helixzz/rdimm-hdd-case/docs/v3.2-rc1.zh-CN.md

# v3.2-rc1：带明确支撑配置的打印可靠性修订

这是针对 v3.1 外壳按压锁扣粘连反馈的**实测中的候选版**。保留 8 条容量、2+3+3 三层一体托盘、147 × 101.6 × 26 mm 外形和按下后滑开的盖板；日常使用仍不需要内部螺丝或独立限位框。此版本没有做提速优化。检查件已打印并拆除全部支撑，但清理依赖工具和技巧；完整套件、锁扣功能、力度及寿命仍未验证。

## 改动

最新实测发现 A 小样缺少下承托，盖板会倾斜下落；弹臂回弹正常。单槽实际 DIMM 装卸无干涉但固定力偏弱。参见 [实物记录](validation-v3.2-rc1.md) 及 [仅修正 A 底座的 RC2](v3.2-rc2-latch-check.zh-CN.md)，不要将原 A 的切片通过等同于锁定功能通过。

1. **外壳锁扣：**移除与弹臂仅隔 0.2 mm 的平行护挡，将弹臂横向宽度从 0.8 增至 1.6 mm。保留根部、锁齿位置和按下释放方向。相邻护挡粘连的几何条件已消除，但弹臂仍需打印支撑；移除护挡也改变了承力方式，不能据此声称携带保持力或疲劳寿命已提高。
2. **托盘槽口：**PCB 支撑高度仍为 3.0 mm，挡齿下表面从 4.5 调整到 4.6 mm；名义槽高从 1.5 增至 1.6 mm。按参考最厚 PCB 1.37 mm，名义高度余量由 0.13 增至 0.23 mm。固定槽和活动齿入口增加约 0.4 mm 长、0.3 mm 高的导入斜面。斜面帮助对准，不表示可以用内存强压扣入。
3. **装配空间：**没有降低底托盘 PCB 支撑面，避免与外壳背板凹区的顶面冲突；没有填死底托盘的背板避让凹区。最不利参考颗粒包络下方仍留约 0.3 mm，向上顶到新止挡时与下一层底面约留 0.1 mm，须用实际内存核对。不得再自行放大槽高或整体缩放。
4. **打印支撑：**工程开启普通贴合支撑，允许支撑从模型表面开始，支撑顶/底 Z 间距 0.2 mm、XY 间距 0.35 mm、顶部接触层 3 层、接触层间距 0.25 mm，同材料打印。逐区检查了外壳弹臂、外壳接口凹区、底托盘约 40 mm 的悬空凹区，以及 8 个槽的固定槽/活动齿下方的支撑路径。

## 文件选择

带 `P2S-PLA-Basic` 后缀的 3MF 是**包含机器、材料、工艺设置的可编辑 Bambu Studio 工程**；需以“打开工程”方式打开，保留配置后切片。它不是已发送的打印任务，也不是 G-code。配套支持配置从本机安装的公开官方预设生成，不含用户打印机连接资料。

仓库 `models/v3.2-rc1/` 的普通 STL/3MF **只含几何**；`profiles/v3.2-rc1-supports.json` 是可复用工艺。不能只导入几何后继续使用关闭支撑的旧工艺。重建带设置工程的方法见下方命令。

| 盘名 | 内容 | P2S / PLA Basic 估算 | 选择方式 |
|---|---|---:|---|
| `plate-0-checks` | 单槽托盘、外壳锁扣底座和滑块、底托盘凹区局部，共 4 件 | 约 31 分钟 / 13.7 g | 可选验证盘，一次打印覆盖主要风险 |
| `plate-1-body-only` | 新外壳 | 约 90 分钟 / 62.7 g | 已有完好 v3.1 盖板时选它 |
| `plate-2-all-trays` | 底/中/顶三张新托盘 | 约 81 分钟 / 46.7 g | 完整托盘盘，只需一次打印 |
| `plate-1-pin-clearance` | 新外壳和盖板 | 约 117 分钟 / 87.0 g | 从零制作整套时选它，替代 body-only |

完整五件仍为 **两盘**；可选验证盘不算生产零件，也不能装入正式盒子。每盘 STL 和 3MF 二选一，不要导入两遍。打印方向已固定，100% 比例，按层打印。

已有 v3.1 盖板的几何不变，可保留并与新外壳试装；旧外壳的失效锁扣不会被新托盘修复。新托盘应使用整套。插入硬盘槽的孔位、接口避让和真实 DIMM 布局仍须实物确认。

上述时间来自 Bambu Studio 02.08.02.61 的切片估算，含估算准备时间，不含换盘、冷却、拆支撑；不是实测承诺。工艺保持 0.20 mm、2 道墙、15% Grid、45° 填充方向、5 层/1.0 mm 顶部、3 层底部与 Classic 墙生成器。PLA Pure 应选择对应的实际耗材预设后重新切片，保留支撑工艺；不能把 PLA Basic 的温度或时间直接当作 PLA Pure 的结果。

## 打印与清理

检查件已实际打印并成功拆除全部支撑；A 接触紧密，B/C 需镊子和技巧，D 尤其小圆点较难清理。功能验证尚未完成。清理时参照 [支撑拆前／拆后对照图](support-removal-v3.2-rc1.zh-CN.md)，不要把原始薄弹臂和台阶当作支撑剪掉；现有试件先检查回弹和装卸，再决定整套打印。

1. 优先打印一盘可选检查件，验证支撑能清理、锁扣能解锁回弹、一个实际 DIMM 能轻柔装卸。若直接打印完整件，它们仍是未实测的候选设计。
2. 打开带设置工程，确认 P2S / 0.4 mm、实际材料以及支撑开启，**“仅在打印板上生成支撑”关闭**。检查切片预览中的支撑，不要以仅导入模型成功作为可以打印的依据。
3. 冷却后清理：外壳弹臂支撑从前侧开口取出；底托盘凹区支撑从底面取出；固定槽和扣齿支撑从朝向内存腔的开口取出。支撑是耗材，不是保留在成品中的限位件。
4. 需要镊子或小钳辅助时夹住支撑，扶住固定框架；不要夹、扭转薄弹臂，不要用 DIMM 撬支撑。若无法在不损伤模型的情况下清理，记录为失败，不强行推进装配。试件已证明可拆，但实际反馈表明仍依赖工具和技巧。
5. 清理完先空扣操作。放内存时，一端送入固定槽，手动向外拨开活动扣，放下 PCB，再松手；不靠内存压斜面自动卡入。无明显阻力、支撑残留、变白或裂纹后再继续。

## 自动检查范围

最终工程已追加 [Bambu Studio 重新切片及实际线宽路径审计](slicing-audit-v3.2-rc1.zh-CN.md)。保留候选状态，不把切片成功等同于支撑易拆或锁扣机械性能验证。

- 512 个参考模块位置、48 个六方向止挡反向检查、2688 个托盘装卸路径位置。
- 新外壳弹臂的 26 个示意释放位置、完整盖板 102 个滑动位置；可选锁扣小样另查闭合和释放路径。
- 两种外壳的装配、三层托盘捕获、26 mm 外形、5 mm 深安装占位、接口避让、可选盖板螺丝占位。
- STL 闭合性、单件连通、3MF 导入回读、排版间距、参考切片及关键区域支撑存在性。

这些检查不预测力、疲劳、蠕变、跌落或运输性能。参考模块仍为 133.8 × 31.4 × 5.57 mm 包络，PCB 厚度 1.17–1.37 mm，两端 2 mm 无元件区仍是待实测假设。普通 PLA 也不是已认证的防静电容器。

## 复现

```powershell
python src/build_v3_2.py --output-dir build/v3.2-rc1
python src/prepare_v3_2_project.py --bambu "C:/Program Files/Bambu Studio/bambu-studio.exe" --profiles "C:/Program Files/Bambu Studio/resources/profiles/BBL"
python src/check_v3_2_supports.py
```

完整官方预设、可编辑带设置工程和 G-code 只生成在本地 `build/`，不提交用户预设或机器路径。固定 v3.1 标签和附件不覆盖；`3.2-rc1` 是新的候选快照，实物结果单独记录。
