helixzz/rdimm-hdd-case/models/v4.1-rc1/body-pin-clearance.stl

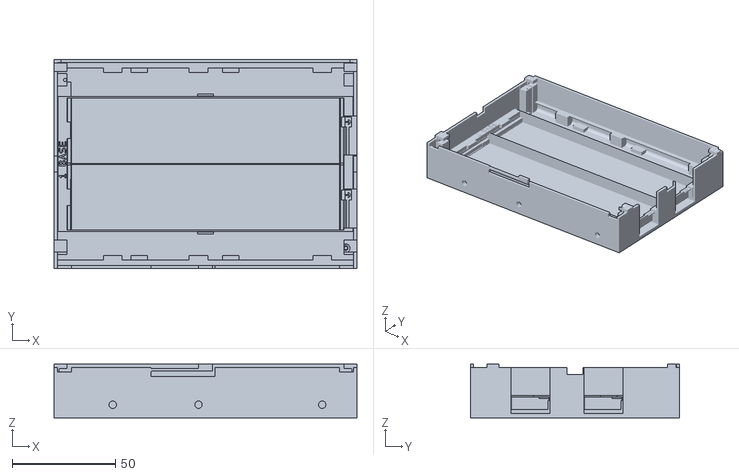
[picture p68: CAD file, 2026-09-29]
models/v4.1-rc1/body-pin-clearance.stl
147.0 x 101.6 x 26.0
