helixzz/rdimm-hdd-case/models/v4.1-rc3/lid-slide-lift.stl

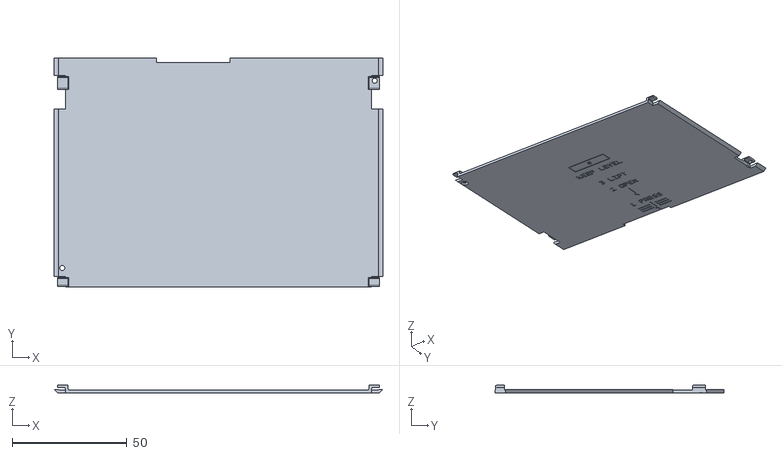
[picture p69: CAD file, 2026-09-29]
models/v4.1-rc3/lid-slide-lift.stl
143.4 x 99.6 x 3.60
