helixzz/rdimm-hdd-case/models/v4.4.1/tray-top-3.stl

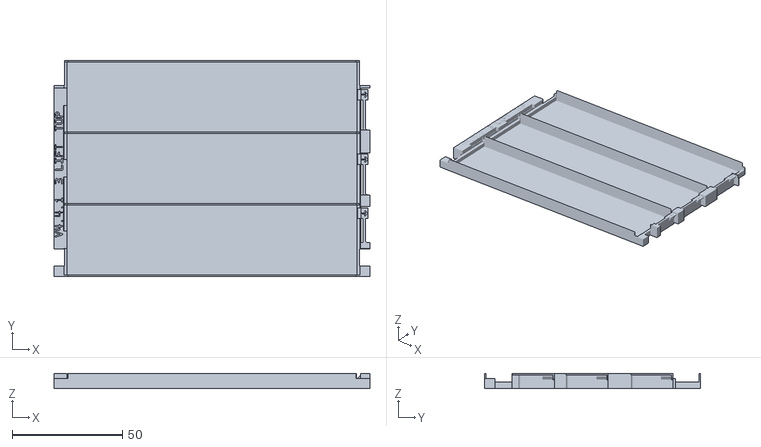
[picture p70: CAD file, 2026-10-05]
models/v4.4.1/tray-top-3.stl
143.2 x 97.8 x 6.80
