helixzz/rdimm-hdd-case/plates/v2/plate-2-middle-top.3mf

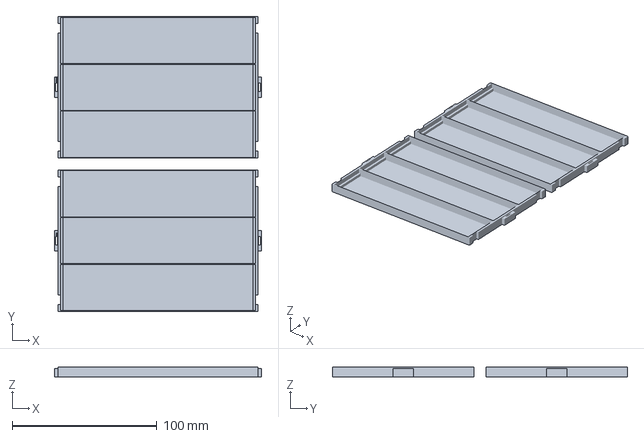
[picture p71: CAD file, 2026-09-28]
plates/v2/plate-2-middle-top.3mf
142.8 x 203.6 x 6.80 mm
