helixzz/rdimm-hdd-case/models/v2-retention/keeper-2-print-2.stl

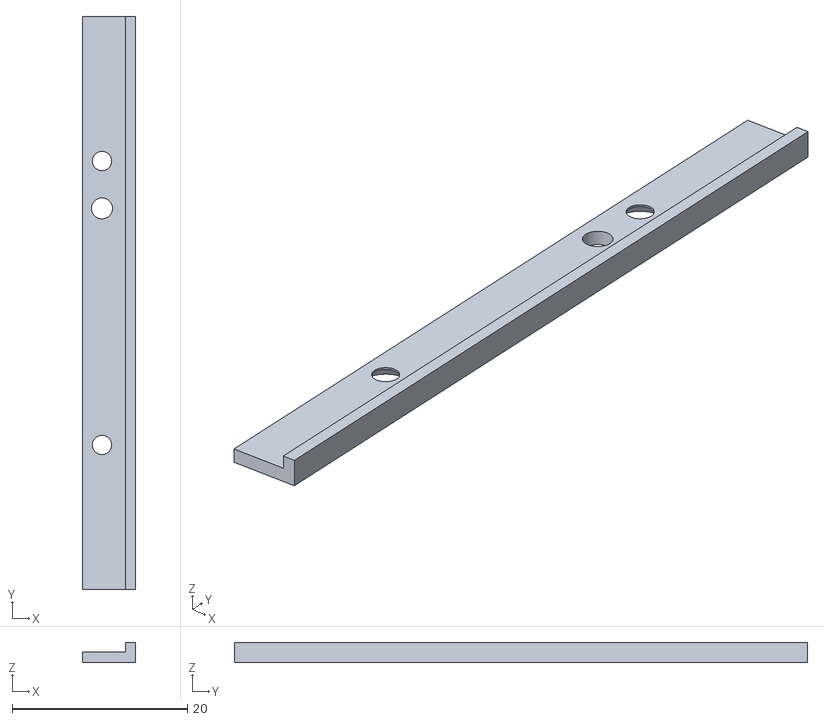
[picture p72: CAD file, 2026-09-29]
models/v2-retention/keeper-2-print-2.stl
6.00 x 65.4 x 2.30
