helixzz/rdimm-hdd-case/models/v4.4-rc1-support-trial/rdimm-4.4-rc1-support-trial-plate-0-support-ab.3mf

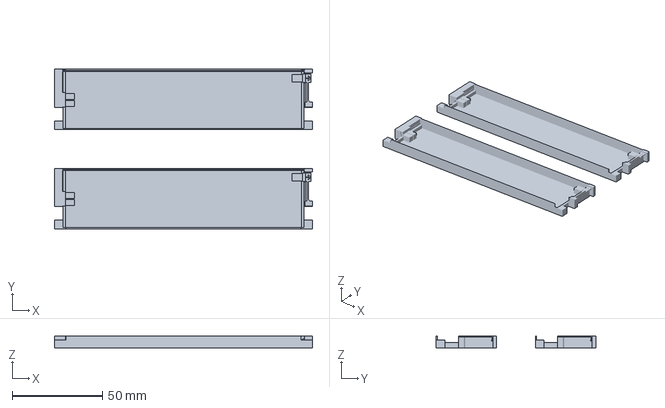
[picture p73: CAD file, 2026-09-30]
models/v4.4-rc1-support-trial/rdimm-4.4-rc1-support-trial-plate-0-support-ab.3mf
143.2 x 88.6 x 6.80 mm
