helixzz/rdimm-hdd-case/plates/v2/optional-test-plate.3mf

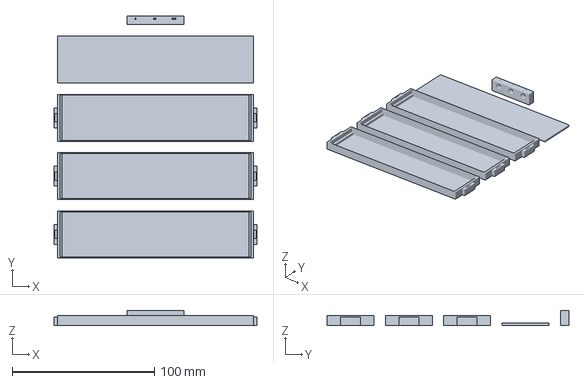
[picture p74: CAD file, 2026-09-28]
plates/v2/optional-test-plate.3mf
142.8 x 170.0 x 10.4 mm
