helixzz/rdimm-hdd-case/models/v2-retention/upgrade-plate-1-lid-bottom-keepers.stl

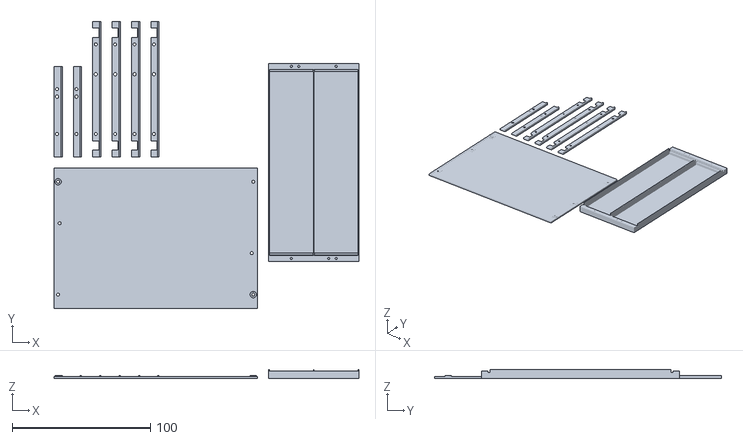
[picture p75: CAD file, 2026-09-29]
models/v2-retention/upgrade-plate-1-lid-bottom-keepers.stl
220.4 x 207.4 x 6.80
