helixzz/rdimm-hdd-case/models/v2-retention/test-tray-1.stl

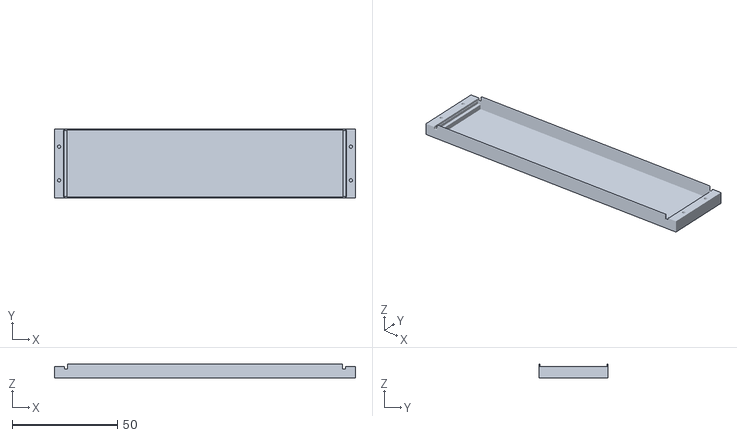
[picture p76: CAD file, 2026-09-29]
models/v2-retention/test-tray-1.stl
143.2 x 33.0 x 6.80
