helixzz/rdimm-hdd-case/models/v2-retention/test-keeper-1-print-2.stl

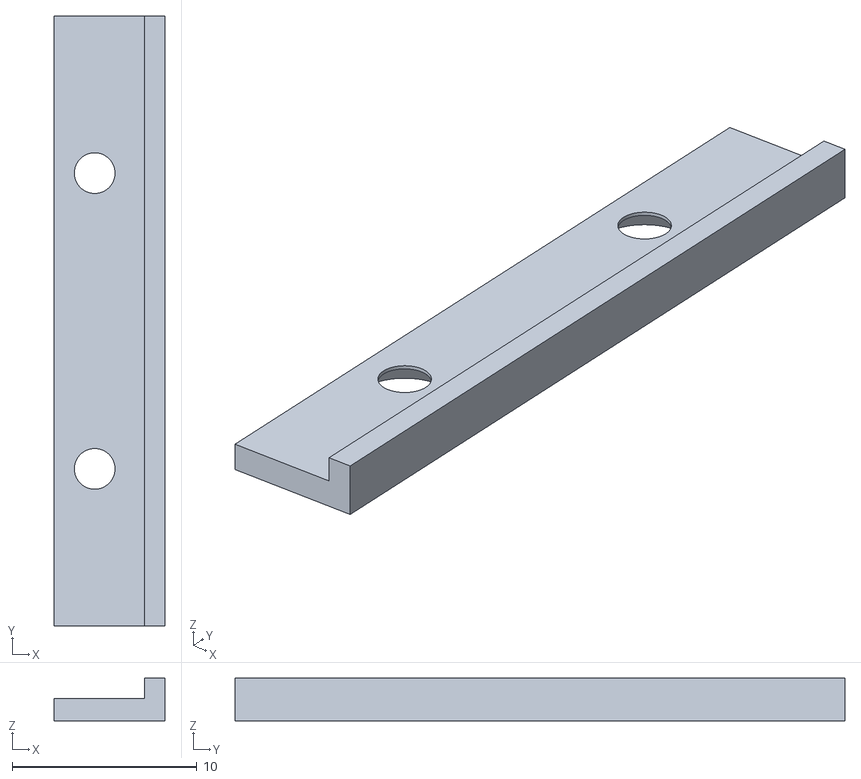
[picture p77: CAD file, 2026-09-29]
models/v2-retention/test-keeper-1-print-2.stl
6.00 x 33.0 x 2.30
