helixzz/rdimm-hdd-case/models/v2-retention/upgrade-plate-2-middle-top.stl

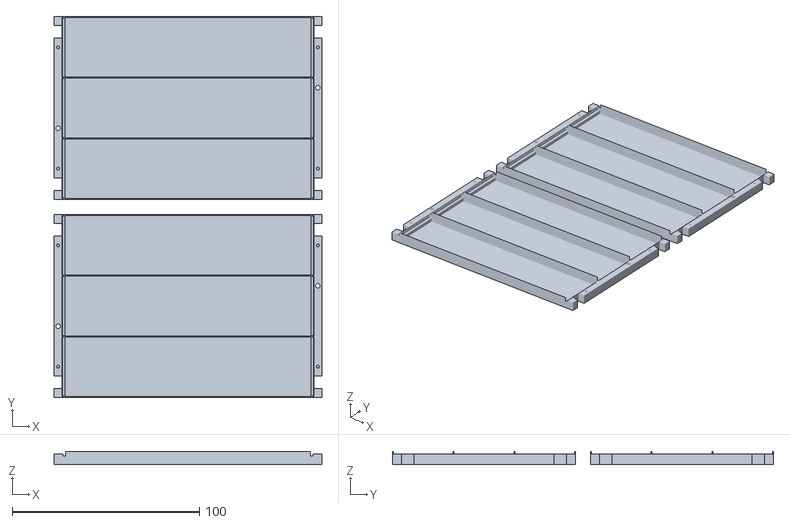
[picture p78: CAD file, 2026-09-29]
models/v2-retention/upgrade-plate-2-middle-top.stl
143.2 x 203.6 x 6.80
