helixzz/rdimm-hdd-case/models/v2-retention/keeper-3-print-4.stl

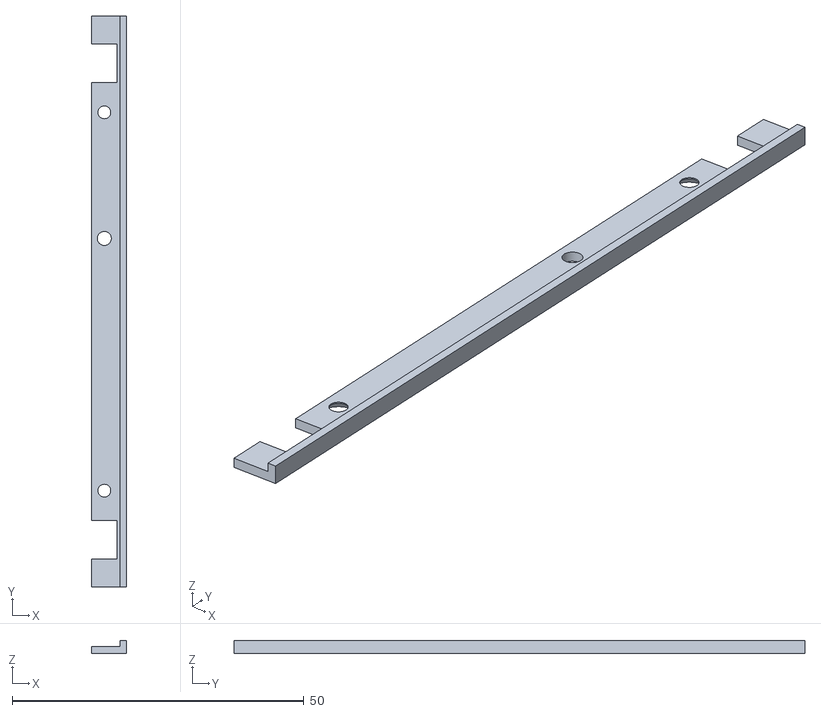
[picture p79: CAD file, 2026-09-29]
models/v2-retention/keeper-3-print-4.stl
6.00 x 97.8 x 2.30
