helixzz/rdimm-hdd-case/models/v2-retention/first-test-plate.stl

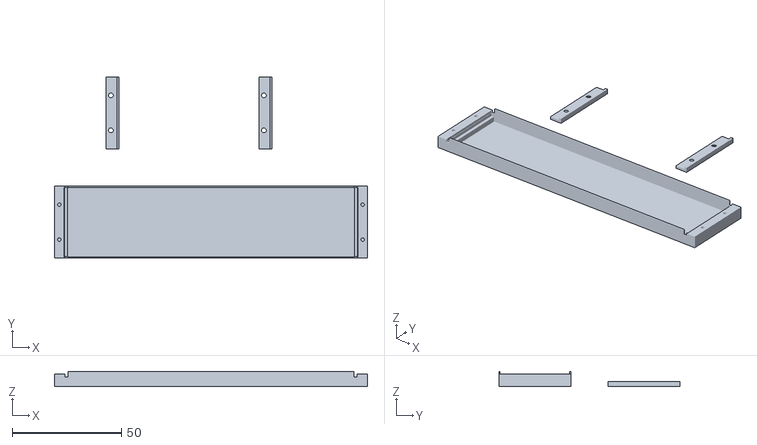
[picture p80: CAD file, 2026-09-29]
models/v2-retention/first-test-plate.stl
143.2 x 83.0 x 6.80
